srkovnar/wherehouse/subsystems/communication/inc/communication.h

// VERSION 1.0.0

#ifndef H_COMMUNICATION
#define H_COMMUNICATION

#include <Arduino.h>

#define MAX_SSID_LENGTH         32
#define MAX_PASSWORD_LENGTH     32
#define MAX_IP_LENGTH           16

#define MAX_STRING_LENGTH       32

#define EEPROM_START_ADDRESS    0

#endif // H_COMMUNICATION
