srkovnar/wherehouse/subsystems/communication/stm32_firmware/stm32_comms_3/src/tty.c

#include "stm32f0xx.h"

#include <stdio.h>
#include "tty.h"
#include "fifo.h"

struct fifo input_fifo;  // input buffer
//int echo_mode = 1;       // should we echo input characters?
int echo_mode = 0;
int line_mode = 1;       // should we wait for a newline?

//=======================================================================
// Simply write a string one char at a time.
//=======================================================================
static void putstr(const char *s) {
    while(*s)
        __io_putchar(*s++);
}

//=======================================================================
// Insert a character and echo it.
// (or, if it's a backspace, remove a char and erase it from the line).
// If echo_mode is turned off, just insert the character and get out.
//=======================================================================
void insert_echo_char(char ch) {
    if (ch == '\r')
        ch = '\n';
    if (!echo_mode) {
        fifo_insert(&input_fifo, ch);
        return;
    }
    if (ch == '\b' || ch == '\177') {
        if (!fifo_empty(&input_fifo)) {
            char tmp = fifo_uninsert(&input_fifo);
            if (tmp == '\n')
                fifo_insert(&input_fifo, '\n');
            else if (tmp < 32)
                putstr("\b\b  \b\b");
            else
                putstr("\b \b");
        }
        return; // Don't put a backspace into buffer.
    } else if (ch == '\n') {
        __io_putchar('\n');
    } else if (ch == 0){
        putstr("^0");
    } else if (ch == 28) {
        putstr("^\\");
    } else if (ch < 32) {
        __io_putchar('^');
        __io_putchar('A'-1+ch);
    } else {
        __io_putchar(ch);
    }
    fifo_insert(&input_fifo, ch);
}


int line_buffer_getchar(void) {
    USART_TypeDef *u = USART5;
    // If we missed reading some characters, clear the overrun flag.
    if (u->ISR & USART_ISR_ORE)
        u->ICR |= USART_ICR_ORECF;
    // Wait for a newline to complete the buffer.
    while(fifo_newline(&input_fifo) == 0) {
        while (!(u->ISR & USART_ISR_RXNE))
            ;
        insert_echo_char(u->RDR);
    }
    // Return a character from the line buffer.
    char ch = fifo_remove(&input_fifo);
    return ch;
}

void raw_mode(void)
{
    line_mode = 0;
    echo_mode = 0;
}

void cooked_mode(void)
{
    line_mode = 1;
    echo_mode = 1;
}

int tty_input_available(void)
{
    if (line_mode)
        return fifo_newline(&input_fifo);
    if (!fifo_empty(&input_fifo))
        return 1;
    if ((USART5->ISR & USART_ISR_RXNE) == 0)
        return 0;
    return 1;
}
